tristanseifert/NixieClock/Emulator/src/Emulator.h

#ifndef EMULATOR_H
#define EMULATOR_H

#include <string>
#include <atomic>
#include <cstdint>
#include <iostream>

class MC68681;
class TubeDrivers;
class VFD;
class DS1244;

class Emulator {
  public:
    class M68kRegs {
      public:
        /// data registers
        uint32_t d0 = 0, d1 = 0, d2 = 0, d3 = 0, d4 = 0, d5 = 0, d6 = 0, d7 = 0;
        /// address registers
        uint32_t a0 = 0, a1 = 0, a2 = 0, a3 = 0, a4 = 0, a5 = 0, a6 = 0, a7 = 0;
        /// program counter
        uint32_t pc = 0;
        /// status register
        uint32_t sr = 0;

      friend std::ostream& operator<<(std::ostream& os, const M68kRegs& dt);
    };

  public:
    Emulator(std::string romFilePath, std::string nvramFilePath);
    ~Emulator();

    void start(void);
    void stop(void);

    void getRegs(M68kRegs &regs);

  private:
    void loadROM(const std::string path);
    void loadNVRAM(const std::string path);

  public:
    void cpuExecutedInstruction(uint64_t address);
    void cpuHookMem(bool read, uint64_t addr, int size, int64_t value);
    void cpuInt(uint32_t intno);

  private:
    uint32_t initialPc = 0, initialSp = 0;

    std::atomic_bool run = true;

    MC68681 *duart = nullptr;
    TubeDrivers *tubes = nullptr;
    VFD *vfd = nullptr;
    DS1244 *rtc = nullptr;

    uint8_t memRom[0x20000];
    uint8_t memRam[0x20000];

    uint8_t nvram[0x8000];

  private:
    friend void *Get68kBuffer(bool, uint32_t);
    friend int Handle68kPeriph(bool, uint8_t, uint32_t, uint32_t *);
    friend void Unhandled68kTransaction(bool, uint32_t, uint32_t, int);
};

#endif
